rweather/generic-front-panel/schematics/Generic_Front_Panel/Generic_Front_Panel.kicad_pcb

## KiCad design schematics/Generic_Front_Panel/Generic_Front_Panel.kicad_pcb (2025-05-16)

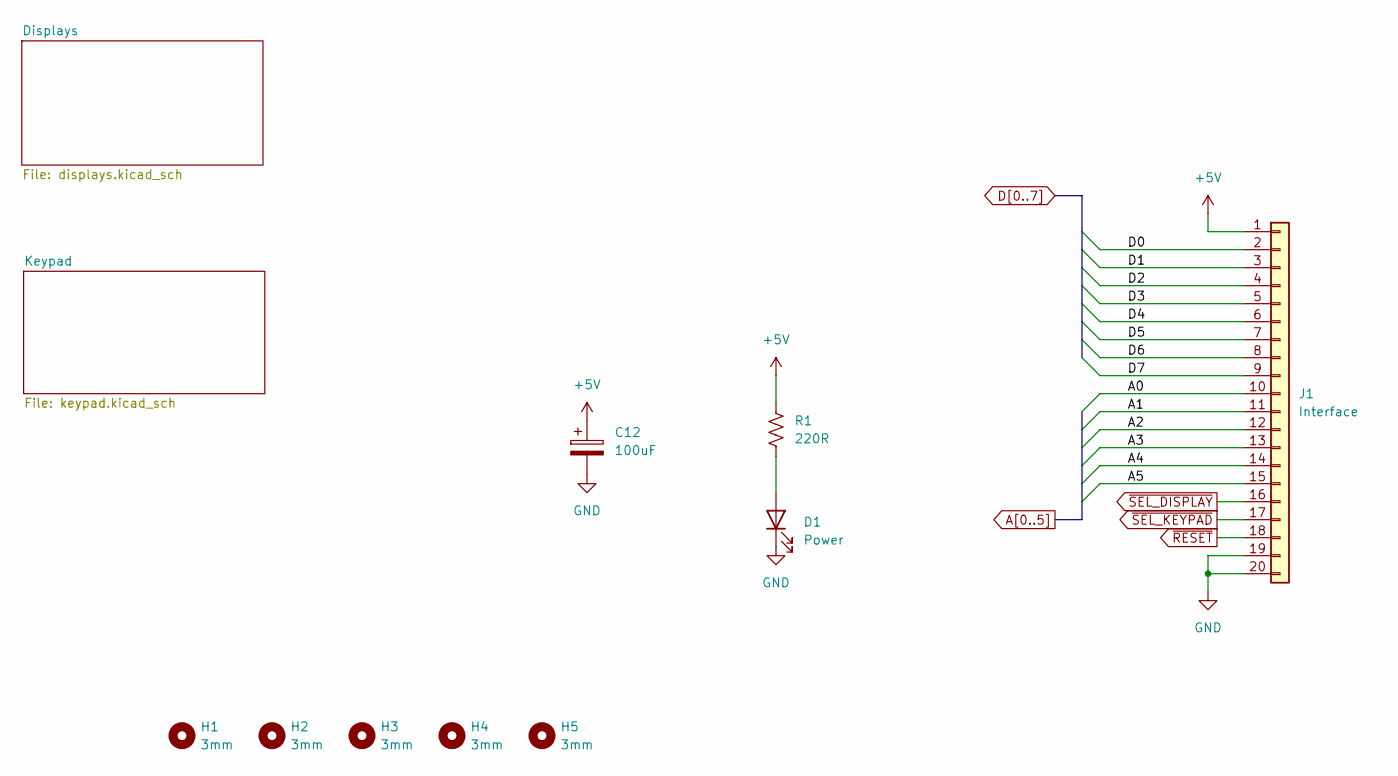
[picture p10: schematic Generic_Front_Panel.kicad_sch, Generic Front Panel FP-01]

Parts:
C12: 100uF; CP_Radial_D6.3mm_P2.50mm
D1: Power; LED_D5.0mm
H1, H2, H3, H4, H5: 3mm; MountingHole_3mm
J1: Interface; PinSocket_1x20_P2.54mm_Vertical
R1: 220R; R_Axial_DIN0207_L6.3mm_D2.5mm_P10.16mm_Horizontal

Connections:
+5V: C12.1, J1.1, R1.1; also elsewhere on the board
A0: J1.10; also elsewhere on the board
A1: J1.11; also elsewhere on the board
A2: J1.12; also elsewhere on the board
A3: J1.13; also elsewhere on the board
A4: J1.14; also elsewhere on the board
A5: J1.15; also elsewhere on the board
D0: J1.2; also elsewhere on the board
D1: J1.3; also elsewhere on the board
D2: J1.4; also elsewhere on the board
D3: J1.5; also elsewhere on the board
D4: J1.6; also elsewhere on the board
D5: J1.7; also elsewhere on the board
D6: J1.8; also elsewhere on the board
D7: J1.9; also elsewhere on the board
GND: C12.2, D1.1 (K), J1.19, J1.20; also elsewhere on the board
unnamed: D1.2 (A), R1.2
~RESET: J1.18; also elsewhere on the board
~SEL_DISPLAY: J1.16; also elsewhere on the board
~SEL_KEYPAD: J1.17; also elsewhere on the board

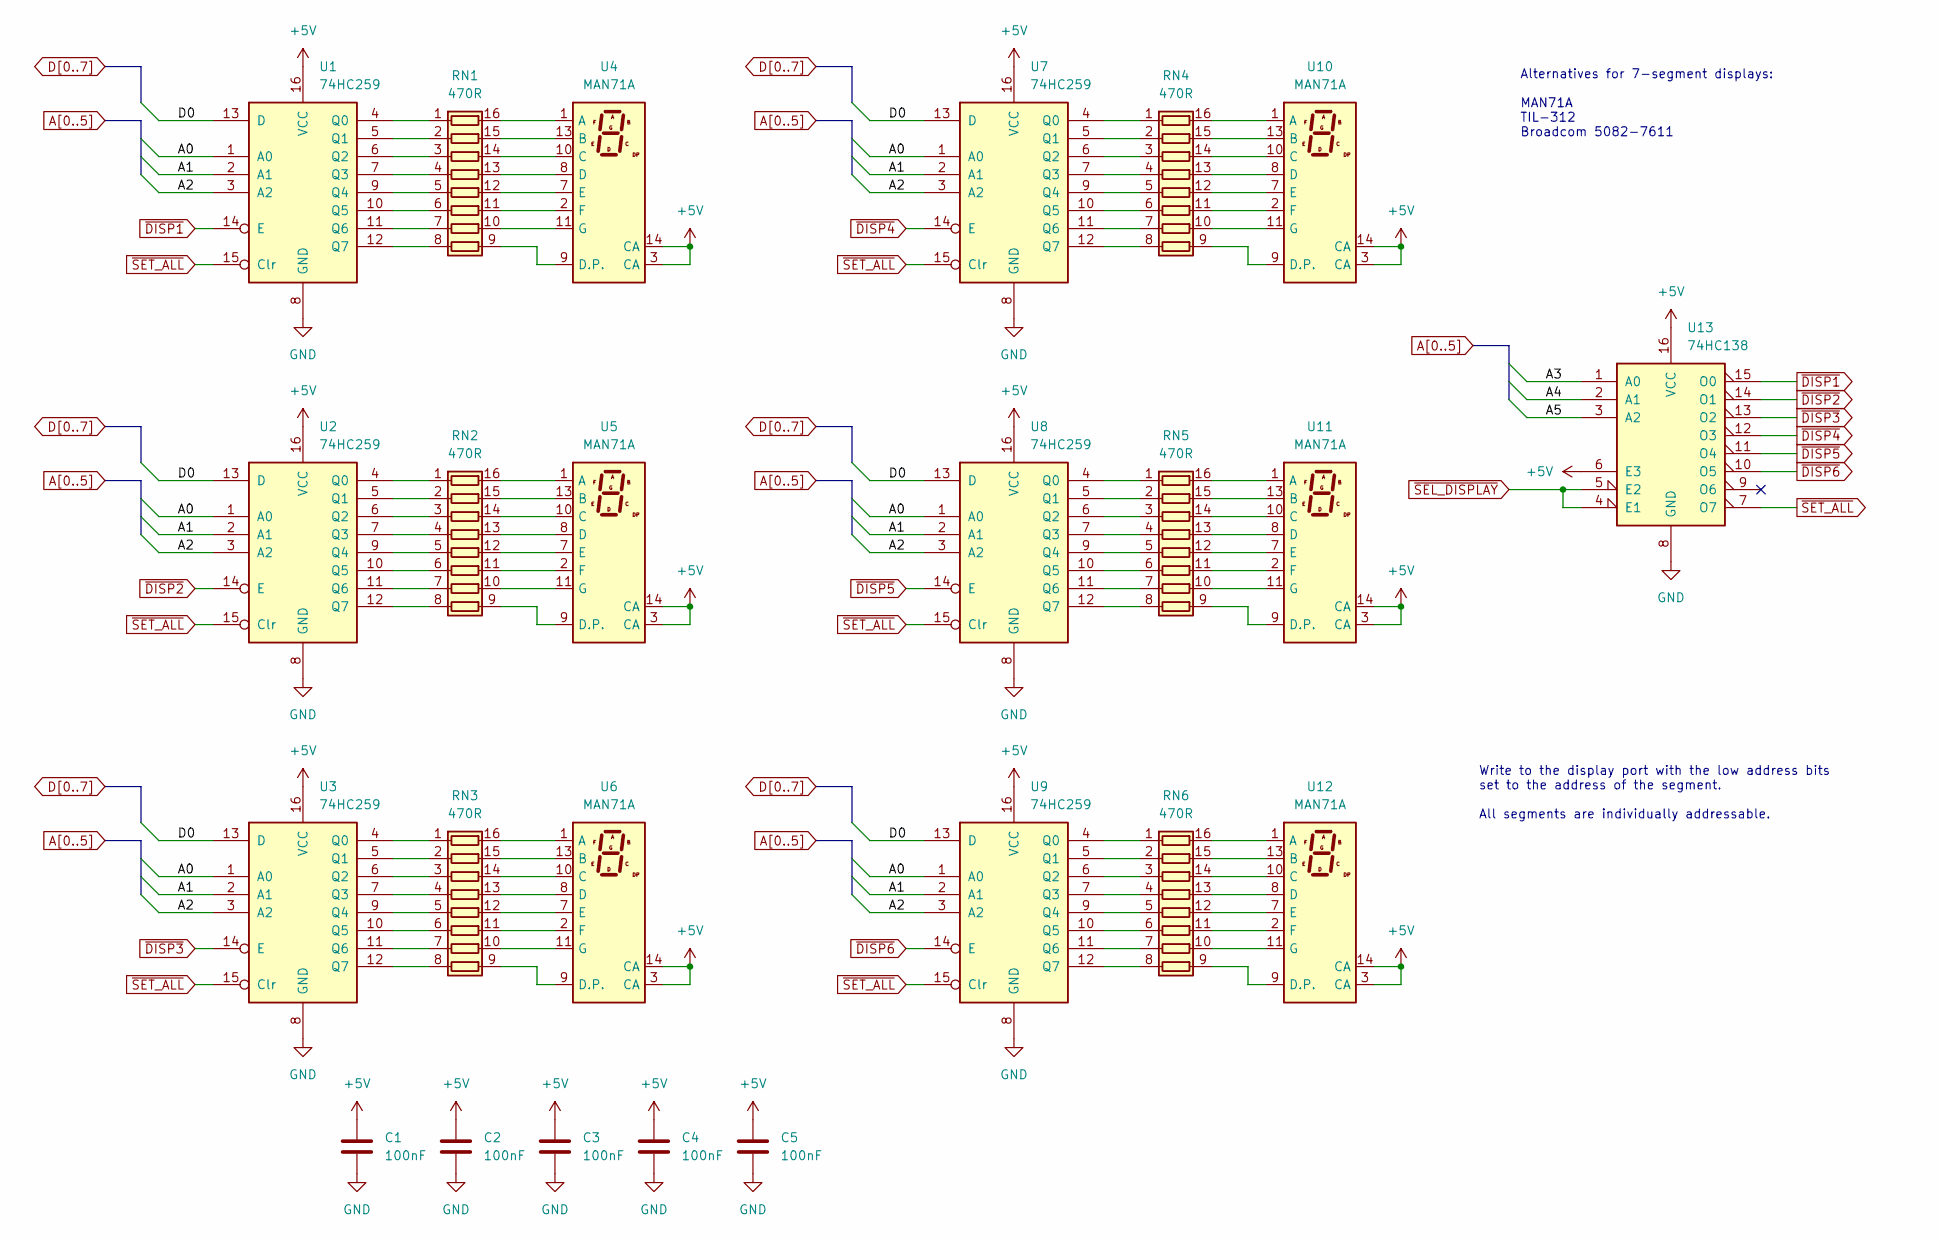
[picture p11: schematic displays.kicad_sch, Generic Front Panel FP-01]

Parts:
C1, C2, C3, C4, C5: 100nF; C_Disc_D6.0mm_W2.5mm_P5.00mm
RN1, RN2, RN3, RN4, RN5, RN6: 470R; DIP-16_W7.62mm
U1, U2, U3, U7, U8, U9: 74HC259; DIP-16_W7.62mm
U4, U5, U6, U10, U11, U12: MAN71A
U13: 74HC138; DIP-16_W7.62mm

Connections:
+5V: C1.1, C2.1, C3.1, C4.1, C5.1, U1.16 (VCC), U2.16 (VCC), U3.16 (VCC), U4.3 (CA), U4.14 (CA), U5.3 (CA), U5.14 (CA), U6.3 (CA), U6.14 (CA), U7.16 (VCC), U8.16 (VCC), U9.16 (VCC), U10.3 (CA), U10.14 (CA), U11.3 (CA), U11.14 (CA), U12.3 (CA), U12.14 (CA), U13.6 (E3), U13.16 (VCC); also elsewhere on the board
A0: U1.1 (A0), U2.1 (A0), U3.1 (A0), U7.1 (A0), U8.1 (A0), U9.1 (A0); also elsewhere on the board
A1: U1.2 (A1), U2.2 (A1), U3.2 (A1), U7.2 (A1), U8.2 (A1), U9.2 (A1); also elsewhere on the board
A2: U1.3 (A2), U2.3 (A2), U3.3 (A2), U7.3 (A2), U8.3 (A2), U9.3 (A2); also elsewhere on the board
A3: U13.1 (A0); also elsewhere on the board
A4: U13.2 (A1); also elsewhere on the board
A5: U13.3 (A2); also elsewhere on the board
D0: U1.13 (D), U2.13 (D), U3.13 (D), U7.13 (D), U8.13 (D), U9.13 (D); also elsewhere on the board
GND: C1.2, C2.2, C3.2, C4.2, C5.2, U1.8 (GND), U2.8 (GND), U3.8 (GND), U7.8 (GND), U8.8 (GND), U9.8 (GND), U13.8 (GND); also elsewhere on the board
unnamed: RN1.1 (R1.1), U1.4 (Q0)
unnamed: RN1.16 (R1.2), U4.1 (A)
unnamed: RN1.2 (R2.1), U1.5 (Q1)
unnamed: RN1.15 (R2.2), U4.13 (B)
unnamed: RN1.3 (R3.1), U1.6 (Q2)
unnamed: RN1.14 (R3.2), U4.10 (C)
unnamed: RN1.4 (R4.1), U1.7 (Q3)
unnamed: RN1.13 (R4.2), U4.8 (D)
unnamed: RN1.5 (R5.1), U1.9 (Q4)
unnamed: RN1.12 (R5.2), U4.7 (E)
unnamed: RN1.6 (R6.1), U1.10 (Q5)
unnamed: RN1.11 (R6.2), U4.2 (F)
unnamed: RN1.7 (R7.1), U1.11 (Q6)
unnamed: RN1.10 (R7.2), U4.11 (G)
unnamed: RN1.8 (R8.1), U1.12 (Q7)
unnamed: RN1.9 (R8.2), U4.9 (D.P.)
unnamed: RN2.1 (R1.1), U2.4 (Q0)
unnamed: RN2.16 (R1.2), U5.1 (A)
unnamed: RN2.2 (R2.1), U2.5 (Q1)
unnamed: RN2.15 (R2.2), U5.13 (B)
unnamed: RN2.3 (R3.1), U2.6 (Q2)
unnamed: RN2.14 (R3.2), U5.10 (C)
unnamed: RN2.4 (R4.1), U2.7 (Q3)
unnamed: RN2.13 (R4.2), U5.8 (D)
unnamed: RN2.5 (R5.1), U2.9 (Q4)
unnamed: RN2.12 (R5.2), U5.7 (E)
unnamed: RN2.6 (R6.1), U2.10 (Q5)
unnamed: RN2.11 (R6.2), U5.2 (F)
unnamed: RN2.7 (R7.1), U2.11 (Q6)
unnamed: RN2.10 (R7.2), U5.11 (G)
unnamed: RN2.8 (R8.1), U2.12 (Q7)
unnamed: RN2.9 (R8.2), U5.9 (D.P.)
unnamed: RN3.1 (R1.1), U3.4 (Q0)
unnamed: RN3.16 (R1.2), U6.1 (A)
unnamed: RN3.2 (R2.1), U3.5 (Q1)
unnamed: RN3.15 (R2.2), U6.13 (B)
unnamed: RN3.3 (R3.1), U3.6 (Q2)
unnamed: RN3.14 (R3.2), U6.10 (C)
unnamed: RN3.4 (R4.1), U3.7 (Q3)
unnamed: RN3.13 (R4.2), U6.8 (D)
unnamed: RN3.5 (R5.1), U3.9 (Q4)
unnamed: RN3.12 (R5.2), U6.7 (E)
unnamed: RN3.6 (R6.1), U3.10 (Q5)
unnamed: RN3.11 (R6.2), U6.2 (F)
unnamed: RN3.7 (R7.1), U3.11 (Q6)
unnamed: RN3.10 (R7.2), U6.11 (G)
unnamed: RN3.8 (R8.1), U3.12 (Q7)
unnamed: RN3.9 (R8.2), U6.9 (D.P.)
unnamed: RN4.1 (R1.1), U7.4 (Q0)
unnamed: RN4.16 (R1.2), U10.1 (A)
unnamed: RN4.2 (R2.1), U7.5 (Q1)
unnamed: RN4.15 (R2.2), U10.13 (B)
unnamed: RN4.3 (R3.1), U7.6 (Q2)
unnamed: RN4.14 (R3.2), U10.10 (C)
unnamed: RN4.4 (R4.1), U7.7 (Q3)
unnamed: RN4.13 (R4.2), U10.8 (D)
unnamed: RN4.5 (R5.1), U7.9 (Q4)
unnamed: RN4.12 (R5.2), U10.7 (E)
unnamed: RN4.6 (R6.1), U7.10 (Q5)
unnamed: RN4.11 (R6.2), U10.2 (F)
unnamed: RN4.7 (R7.1), U7.11 (Q6)
unnamed: RN4.10 (R7.2), U10.11 (G)
unnamed: RN4.8 (R8.1), U7.12 (Q7)
unnamed: RN4.9 (R8.2), U10.9 (D.P.)
unnamed: RN5.1 (R1.1), U8.4 (Q0)
unnamed: RN5.16 (R1.2), U11.1 (A)
unnamed: RN5.2 (R2.1), U8.5 (Q1)
unnamed: RN5.15 (R2.2), U11.13 (B)
unnamed: RN5.3 (R3.1), U8.6 (Q2)
unnamed: RN5.14 (R3.2), U11.10 (C)
unnamed: RN5.4 (R4.1), U8.7 (Q3)
unnamed: RN5.13 (R4.2), U11.8 (D)
unnamed: RN5.5 (R5.1), U8.9 (Q4)
unnamed: RN5.12 (R5.2), U11.7 (E)
unnamed: RN5.6 (R6.1), U8.10 (Q5)
unnamed: RN5.11 (R6.2), U11.2 (F)
unnamed: RN5.7 (R7.1), U8.11 (Q6)
unnamed: RN5.10 (R7.2), U11.11 (G)
unnamed: RN5.8 (R8.1), U8.12 (Q7)
unnamed: RN5.9 (R8.2), U11.9 (D.P.)
unnamed: RN6.1 (R1.1), U9.4 (Q0)
unnamed: RN6.16 (R1.2), U12.1 (A)
unnamed: RN6.2 (R2.1), U9.5 (Q1)
unnamed: RN6.15 (R2.2), U12.13 (B)
unnamed: RN6.3 (R3.1), U9.6 (Q2)
unnamed: RN6.14 (R3.2), U12.10 (C)
unnamed: RN6.4 (R4.1), U9.7 (Q3)
unnamed: RN6.13 (R4.2), U12.8 (D)
unnamed: RN6.5 (R5.1), U9.9 (Q4)
unnamed: RN6.12 (R5.2), U12.7 (E)
unnamed: RN6.6 (R6.1), U9.10 (Q5)
unnamed: RN6.11 (R6.2), U12.2 (F)
unnamed: RN6.7 (R7.1), U9.11 (Q6)
unnamed: RN6.10 (R7.2), U12.11 (G)
unnamed: RN6.8 (R8.1), U9.12 (Q7)
unnamed: RN6.9 (R8.2), U12.9 (D.P.)
~DISP1: U1.14 (E), U13.15 (O0)
~DISP2: U2.14 (E), U13.14 (O1)
~DISP3: U3.14 (E), U13.13 (O2)
~DISP4: U7.14 (E), U13.12 (O3)
~DISP5: U8.14 (E), U13.11 (O4)
~DISP6: U9.14 (E), U13.10 (O5)
~SEL_DISPLAY: U13.4 (E1), U13.5 (E2); also elsewhere on the board
~SET_ALL: U1.15 (Clr), U2.15 (Clr), U3.15 (Clr), U7.15 (Clr), U8.15 (Clr), U9.15 (Clr), U13.7 (O7)

Notes on the sheet:
Write to the display port with the low address bits set to the address of the segment. All segments are individually addressable.
Alternatives for 7-segment displays: MAN71A TIL-312 Broadcom 5082-7611

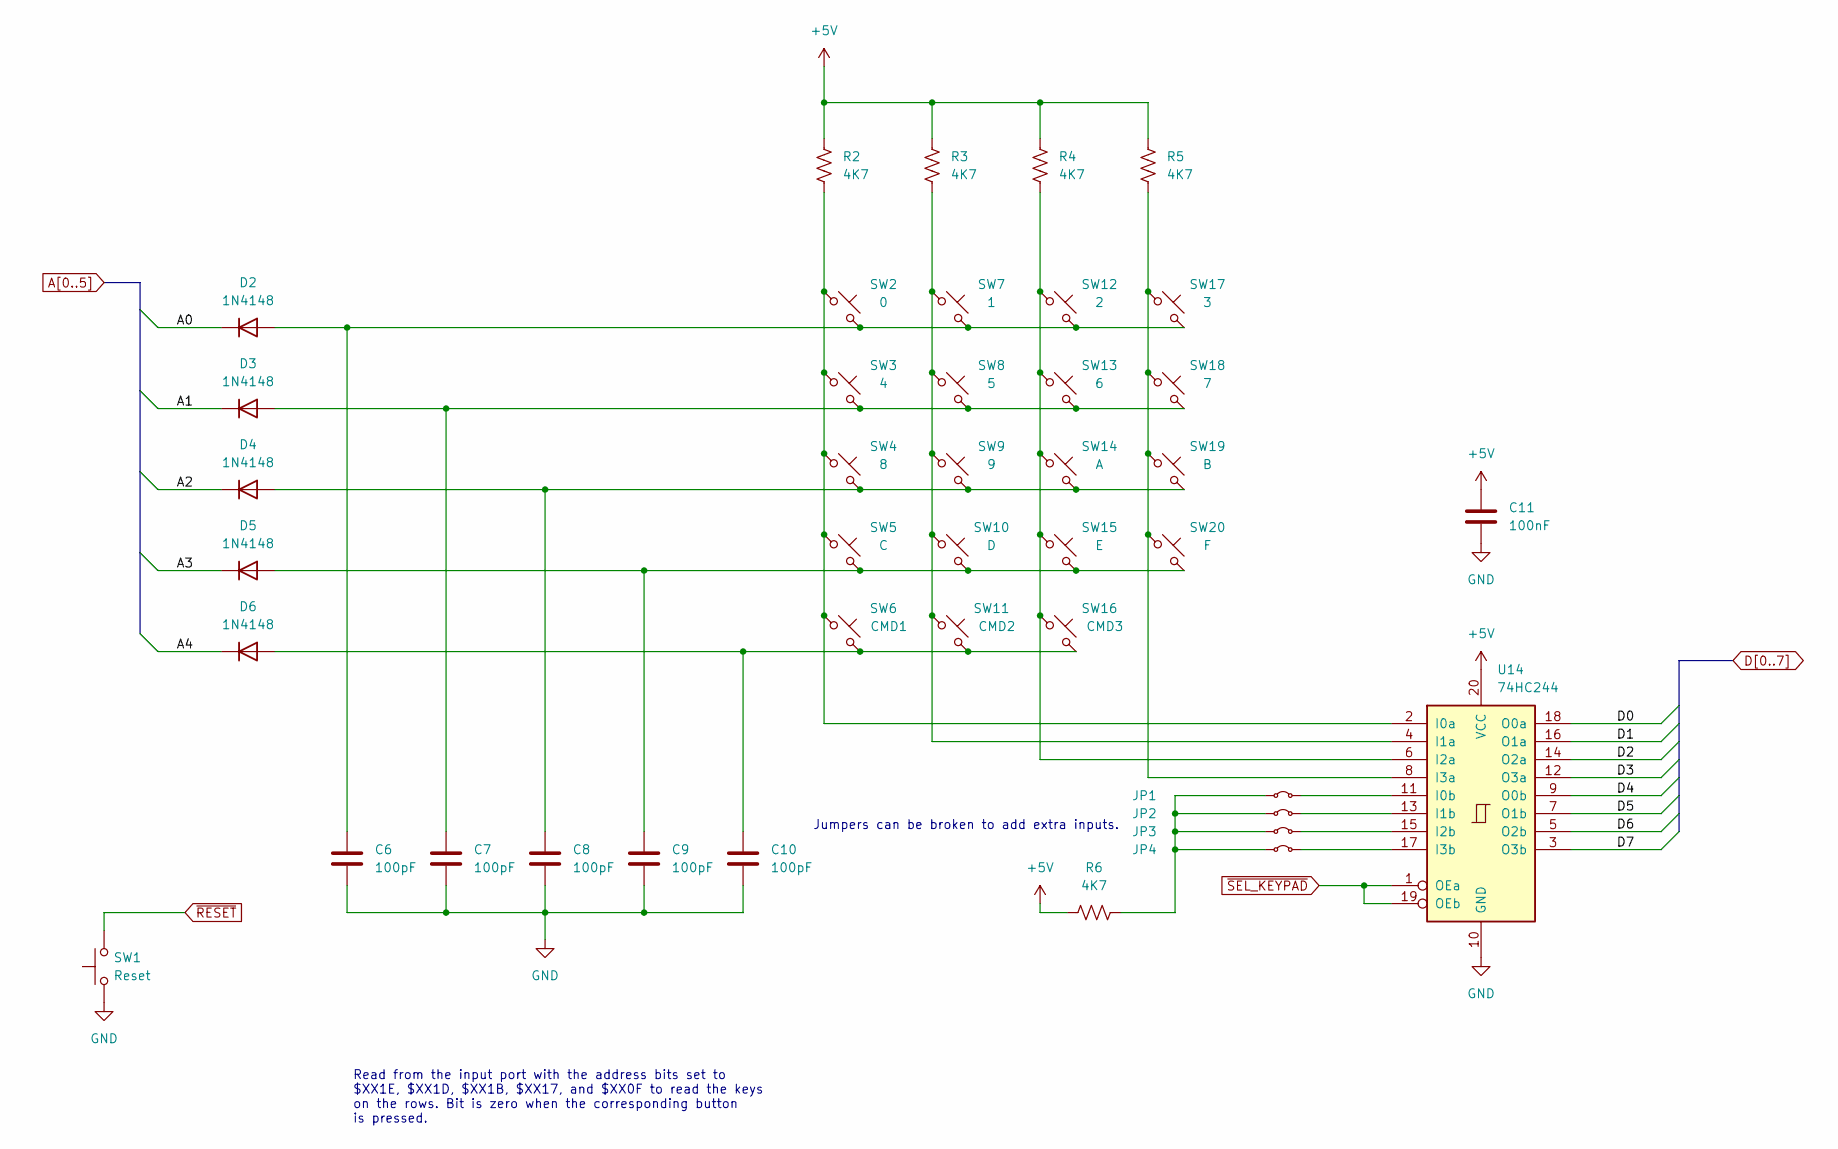
[picture p12: schematic keypad.kicad_sch, Generic Front Panel FP-01]

Parts:
C6, C7, C8, C9, C10: 100pF; C_Disc_D6.0mm_W2.5mm_P5.00mm
C11: 100nF; C_Disc_D6.0mm_W2.5mm_P5.00mm
D2, D3, D4, D5, D6: 1N4148; D_DO-35_SOD27_P7.62mm_Horizontal
JP1, JP2, JP3, JP4: SolderJumper-2_P1.3mm_Bridged_RoundedPad1.0x1.5mm
R2, R3, R4, R5, R6: 4K7; R_Axial_DIN0207_L6.3mm_D2.5mm_P10.16mm_Horizontal
SW1: Reset; SW_PUSH-12mm
SW2: 0; SW_PUSH-12mm
SW3: 4; SW_PUSH-12mm
SW4: 8; SW_PUSH-12mm
SW5: C; SW_PUSH-12mm
SW6: CMD1; SW_PUSH-12mm
SW7: 1; SW_PUSH-12mm
SW8: 5; SW_PUSH-12mm
SW9: 9; SW_PUSH-12mm
SW10: D; SW_PUSH-12mm
SW11: CMD2; SW_PUSH-12mm
SW12: 2; SW_PUSH-12mm
SW13: 6; SW_PUSH-12mm
SW14: A; SW_PUSH-12mm
SW15: E; SW_PUSH-12mm
SW16: CMD3; SW_PUSH-12mm
SW17: 3; SW_PUSH-12mm
SW18: 7; SW_PUSH-12mm
SW19: B; SW_PUSH-12mm
SW20: F; SW_PUSH-12mm
U14: 74HC244; DIP-20_W7.62mm

Connections:
+5V: C11.1, R2.1, R3.1, R4.1, R5.1, R6.1, U14.20 (VCC); also elsewhere on the board
A0: D2.1 (K); also elsewhere on the board
A1: D3.1 (K); also elsewhere on the board
A2: D4.1 (K); also elsewhere on the board
A3: D5.1 (K); also elsewhere on the board
A4: D6.1 (K); also elsewhere on the board
D0: U14.18 (O0a); also elsewhere on the board
D1: U14.16 (O1a); also elsewhere on the board
D2: U14.14 (O2a); also elsewhere on the board
D3: U14.12 (O3a); also elsewhere on the board
D4: U14.9 (O0b); also elsewhere on the board
D5: U14.7 (O1b); also elsewhere on the board
D6: U14.5 (O2b); also elsewhere on the board
D7: U14.3 (O3b); also elsewhere on the board
GND: C6.2, C7.2, C8.2, C9.2, C10.2, C11.2, SW1.1, U14.10 (GND); also elsewhere on the board
unnamed: C6.1, D2.2 (A), SW2.2, SW7.2, SW12.2, SW17.2
unnamed: C7.1, D3.2 (A), SW3.2, SW8.2, SW13.2, SW18.2
unnamed: C8.1, D4.2 (A), SW4.2, SW9.2, SW14.2, SW19.2
unnamed: C9.1, D5.2 (A), SW5.2, SW10.2, SW15.2, SW20.2
unnamed: C10.1, D6.2 (A), SW6.2, SW11.2, SW16.2
unnamed: JP1.1 (A), JP2.1 (A), JP3.1 (A), JP4.1 (A), R6.2
unnamed: JP1.2 (B), U14.11 (I0b)
unnamed: JP2.2 (B), U14.13 (I1b)
unnamed: JP3.2 (B), U14.15 (I2b)
unnamed: JP4.2 (B), U14.17 (I3b)
unnamed: R2.2, SW2.1, SW3.1, SW4.1, SW5.1, SW6.1, U14.2 (I0a)
unnamed: R3.2, SW7.1, SW8.1, SW9.1, SW10.1, SW11.1, U14.4 (I1a)
unnamed: R4.2, SW12.1, SW13.1, SW14.1, SW15.1, SW16.1, U14.6 (I2a)
unnamed: R5.2, SW17.1, SW18.1, SW19.1, SW20.1, U14.8 (I3a)
~RESET: SW1.2; also elsewhere on the board
~SEL_KEYPAD: U14.1 (OEa), U14.19 (OEb); also elsewhere on the board

Notes on the sheet:
Read from the input port with the address bits set to $XX1E, $XX1D, $XX1B, $XX17, and $XX0F to read the keys on the rows. Bit is zero when the corresponding button is pressed.
Jumpers can be broken to add extra inputs.

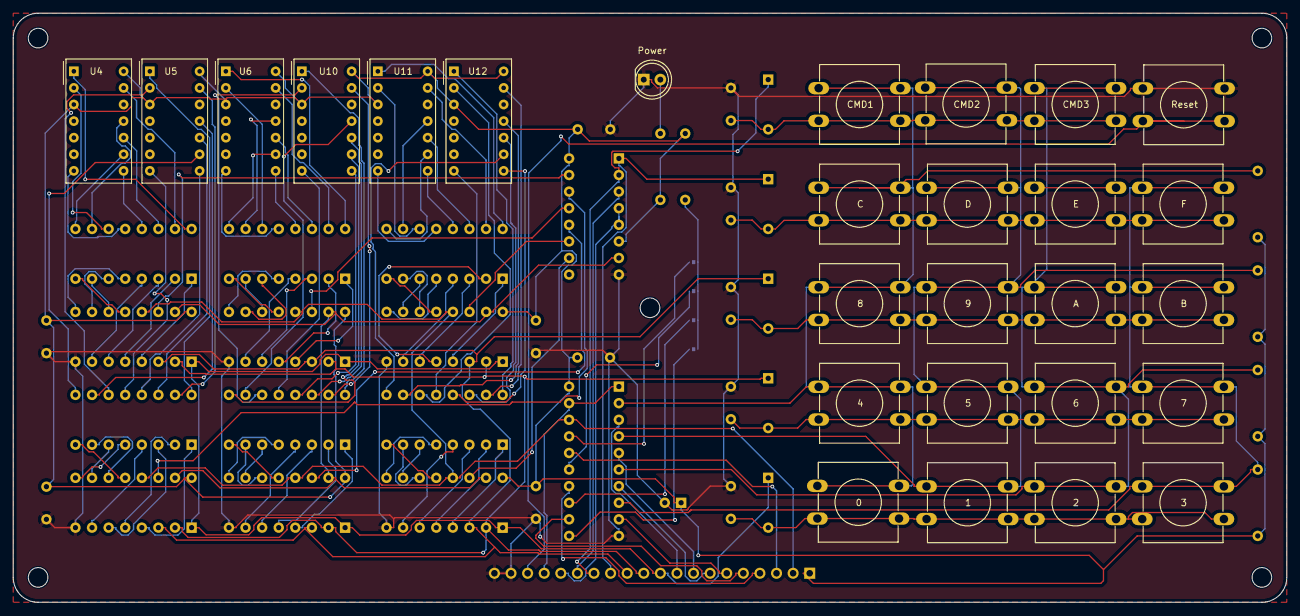
[picture p13: board Generic_Front_Panel.kicad_pcb from above]

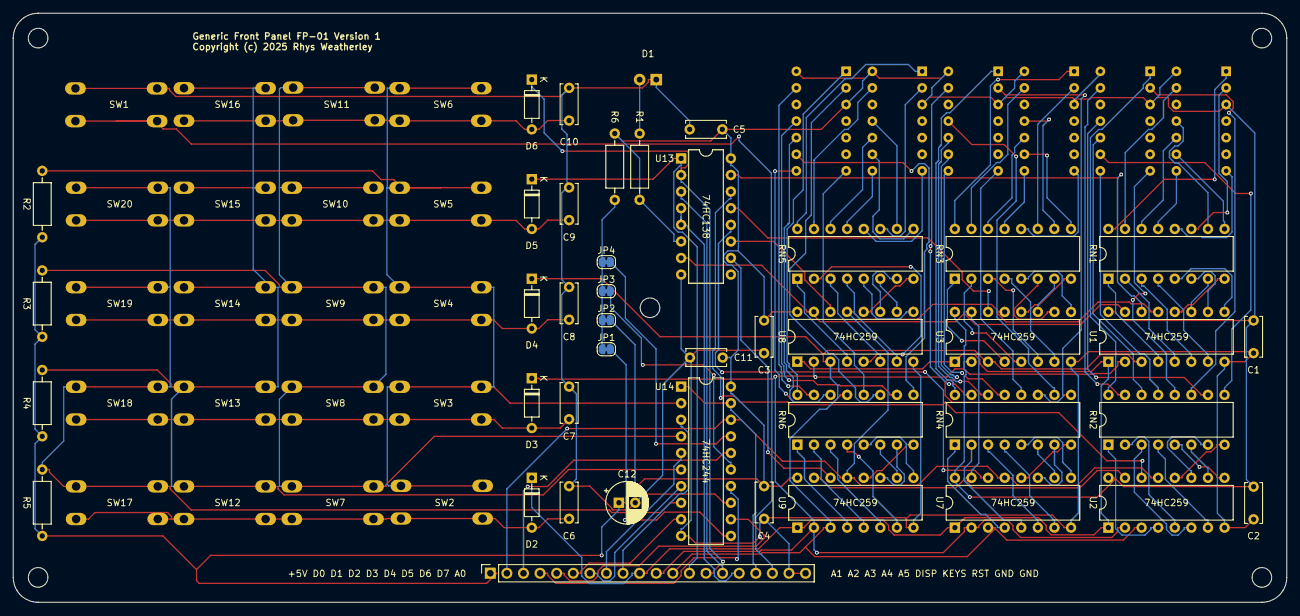
[picture p14: board Generic_Front_Panel.kicad_pcb from below]

Board: 2 copper layers, 194.9 x 90.2 mm, 74 parts (42 on the bottom side), 137 nets.
